MDCservice/EsPiFF/images/cs_weekly/idf_hello_world1.png

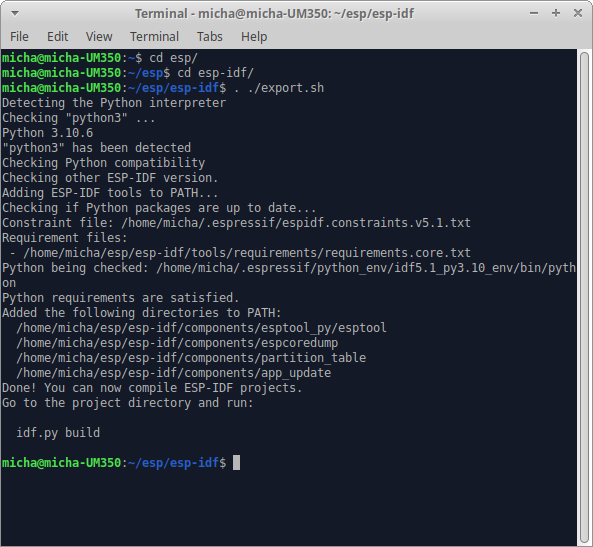
images/cs_weekly/idf_hello_world1.png
