MDCservice/EsPiFF/images/cs_weekly/idf_hello_world2.png

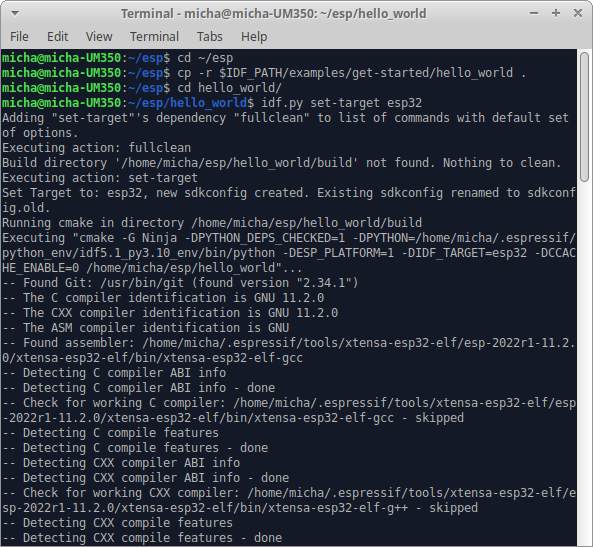
images/cs_weekly/idf_hello_world2.png
