MDCservice/EsPiFF/images/cs_weekly/idf_hello_world3.png

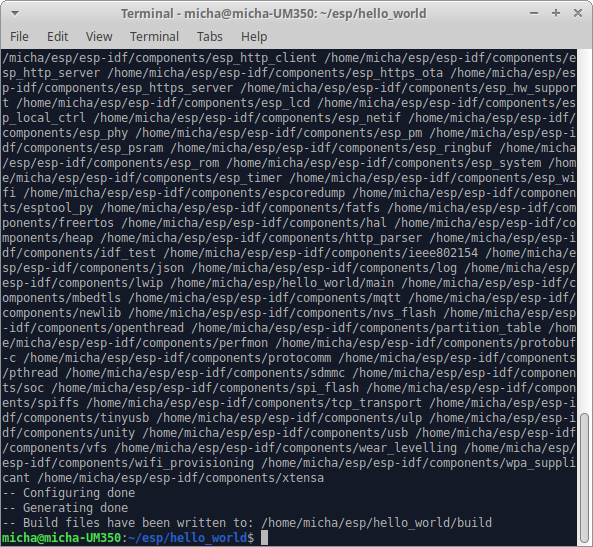
images/cs_weekly/idf_hello_world3.png
