MDCservice/EsPiFF/images/cs_weekly/idf_hello_world4.png

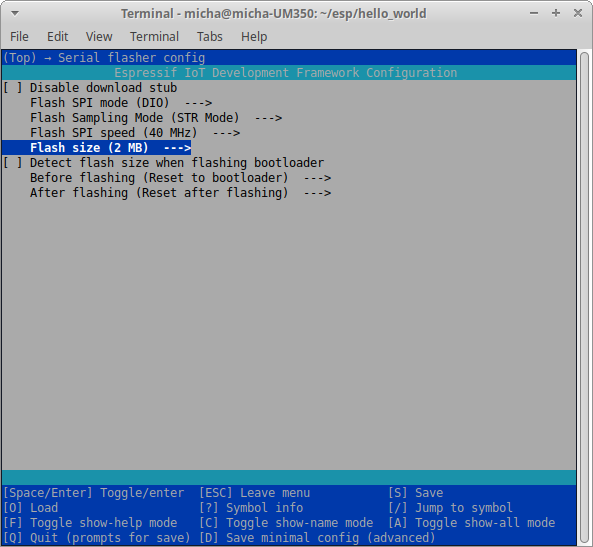
images/cs_weekly/idf_hello_world4.png
