MDCservice/EsPiFF/images/cs_weekly/idf_hello_world6.png

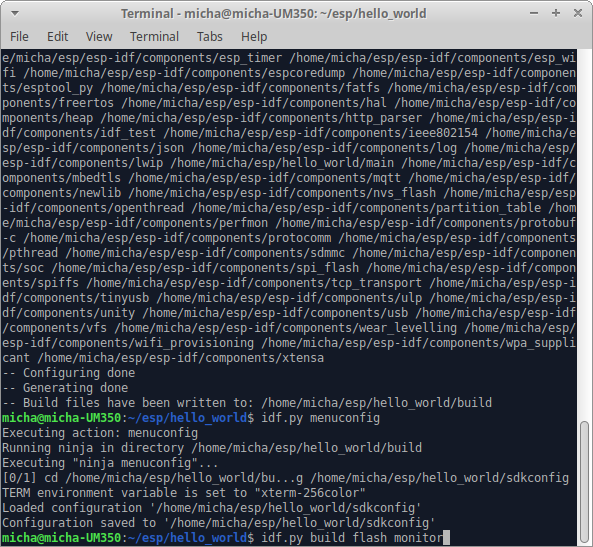
images/cs_weekly/idf_hello_world6.png
