MDCservice/EsPiFF/images/cs_weekly/idf_hello_world7.png

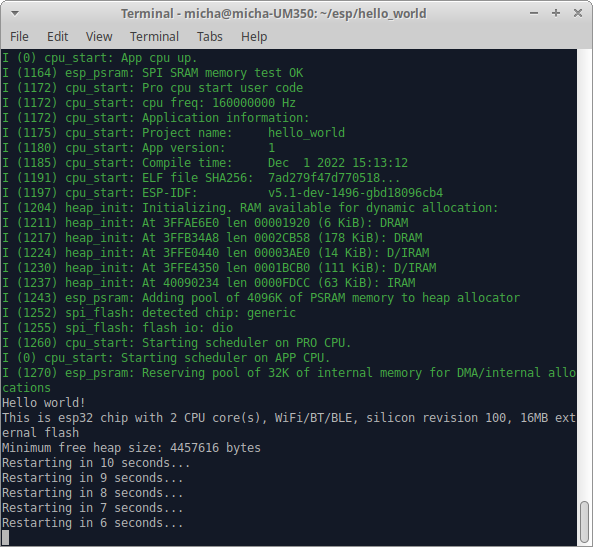
images/cs_weekly/idf_hello_world7.png
