MDCservice/EsPiFF/images/espiff_autoWeiss.jpg

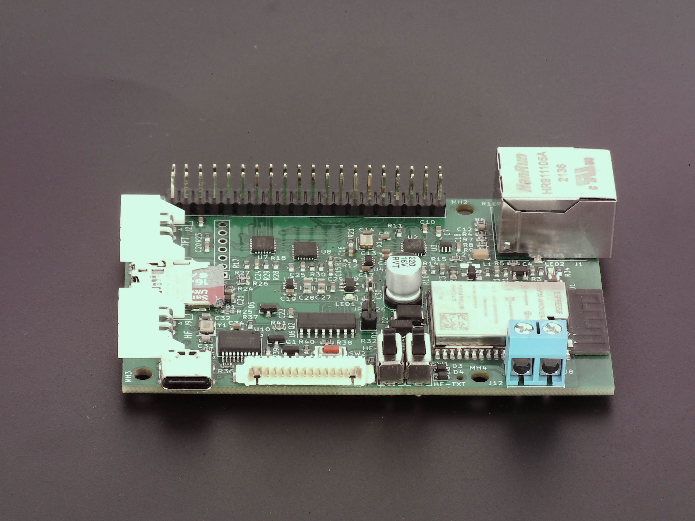
images/espiff_autoWeiss.jpg
