MDCservice/EsPiFF/images/Espiff_boot_nuttx.png

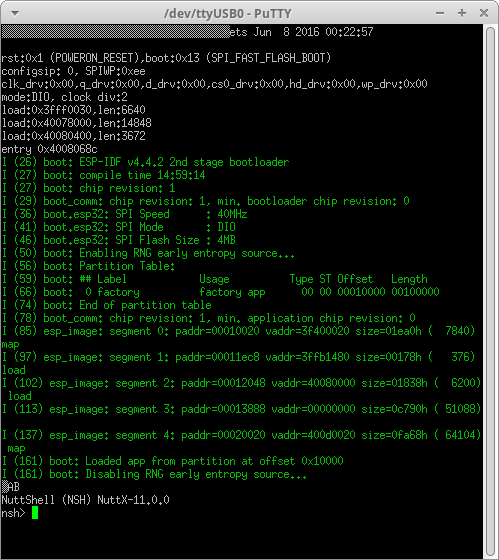
images/Espiff_boot_nuttx.png
