MDCservice/EsPiFF/images/espiff_HMI_horiz.jpg

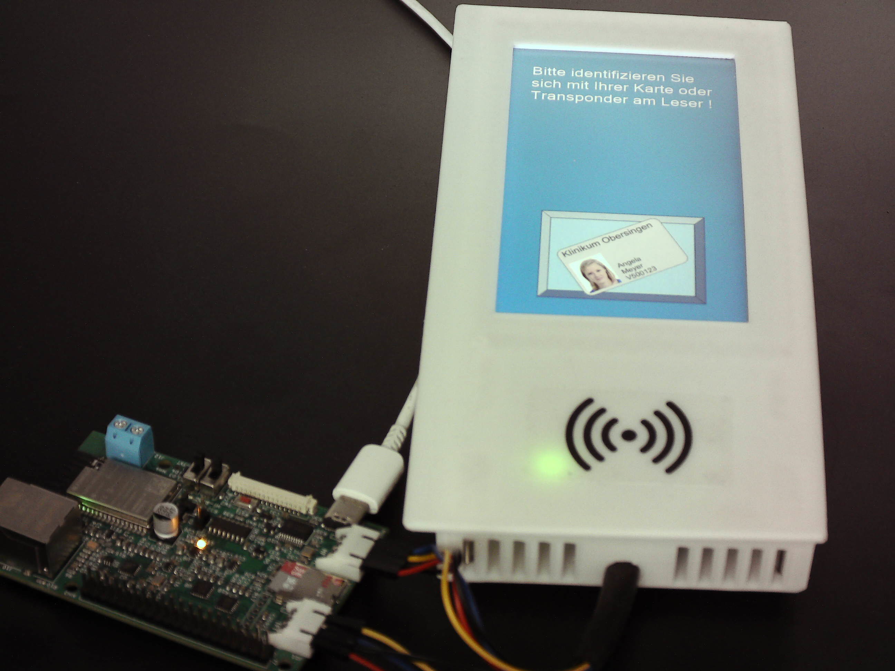
images/espiff_HMI_horiz.jpg
