MDCservice/EsPiFF/images/EsPiFF_PLC_Loop_compare.png

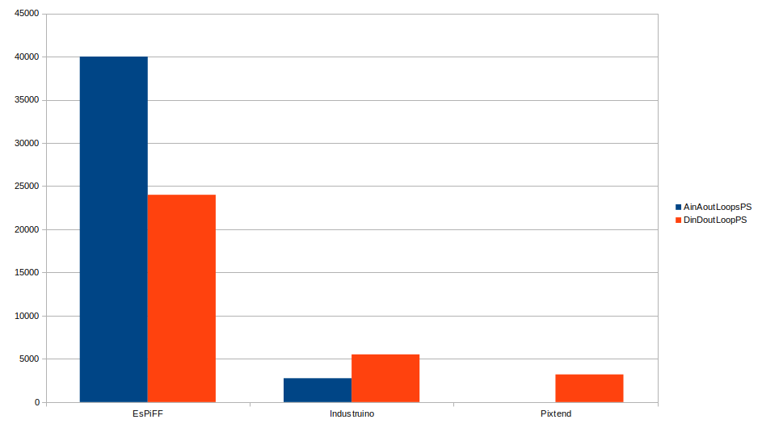
images/EsPiFF_PLC_Loop_compare.png
