MDCservice/EsPiFF/images/espiff_v3_1_annotated.png

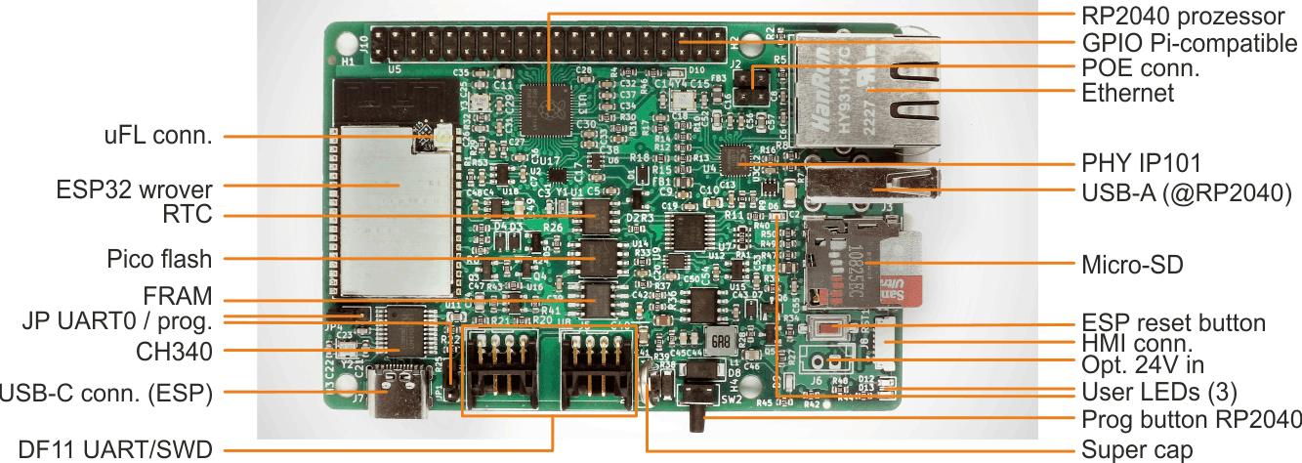
images/espiff_v3_1_annotated.png
