MDCservice/EsPiFF/images/espiff_v3_board-annotated-400.png

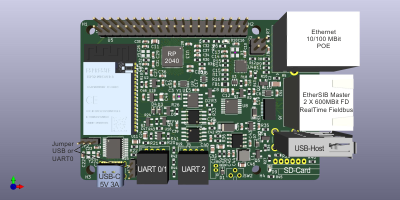
images/espiff_v3_board-annotated-400.png
