MDCservice/EsPiFF/images/espiff_v3_winkel.jpg

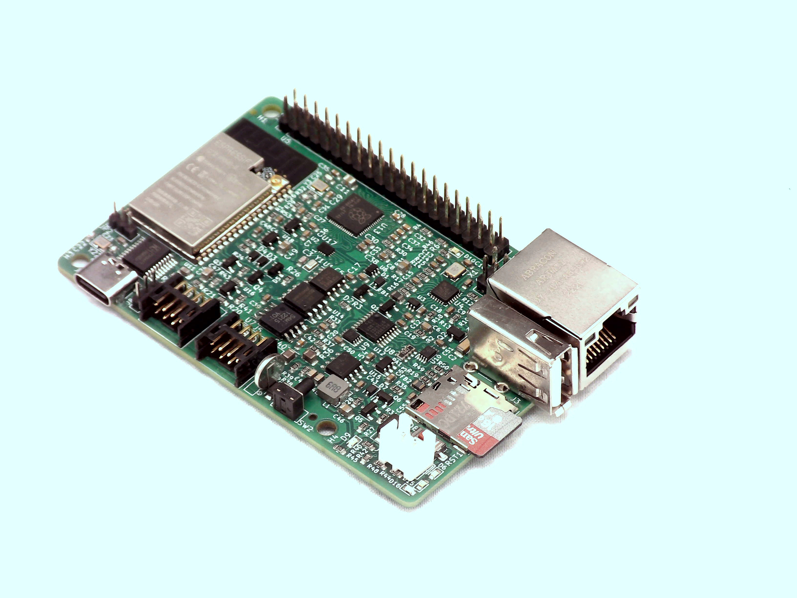
images/espiff_v3_winkel.jpg
