MDCservice/EsPiFF/images/usb_desciptor_c_after_mod.png

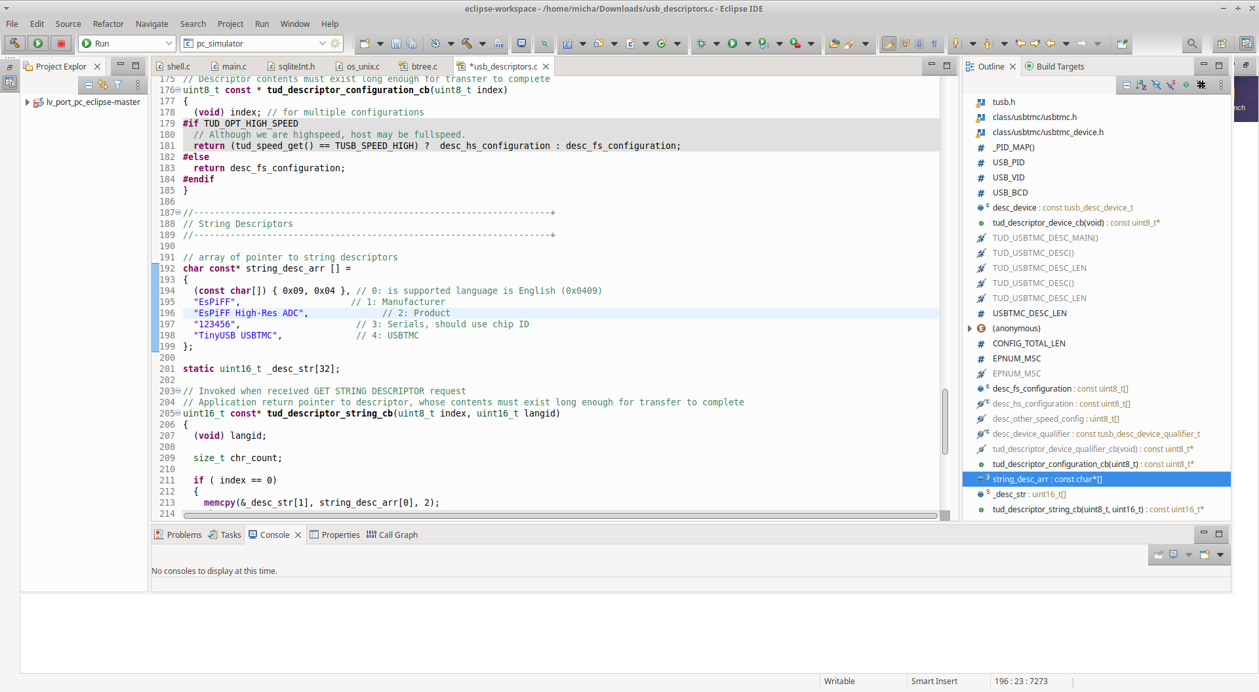
images/usb_desciptor_c_after_mod.png
