MDCservice/EsPiFF/images/v3_1_crowd_supply/espiff_v3.1-angled-0.jpg

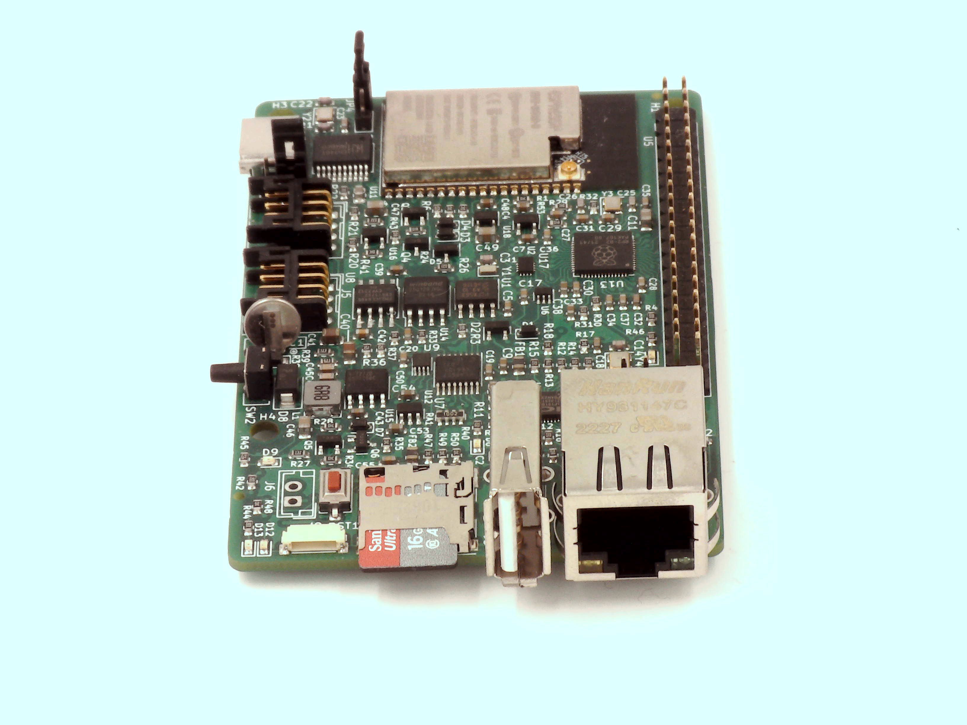
images/v3_1_crowd_supply/espiff_v3.1-angled-0.jpg
