MDCservice/EsPiFF/images/espiff_manualWeiss.jpg

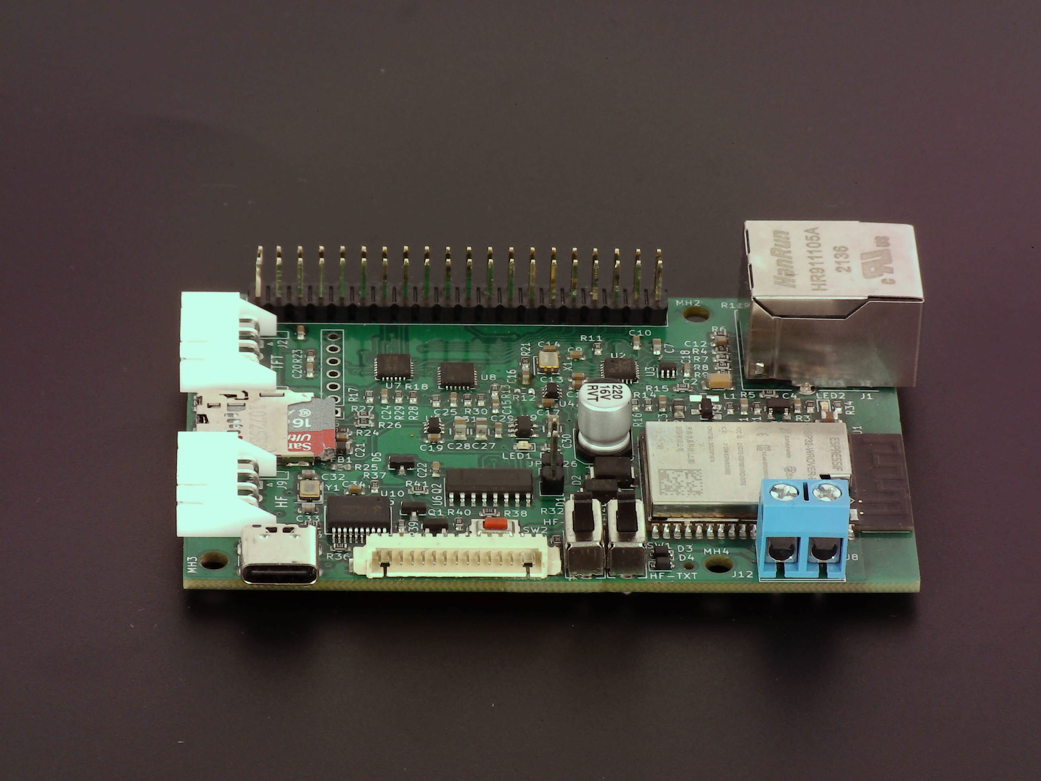
images/espiff_manualWeiss.jpg
