MDCservice/EsPiFF/hardware/espiff_v3_1.kicad_sch

## KiCad design hardware/espiff_v3_1.kicad_sch (2022-10-01)

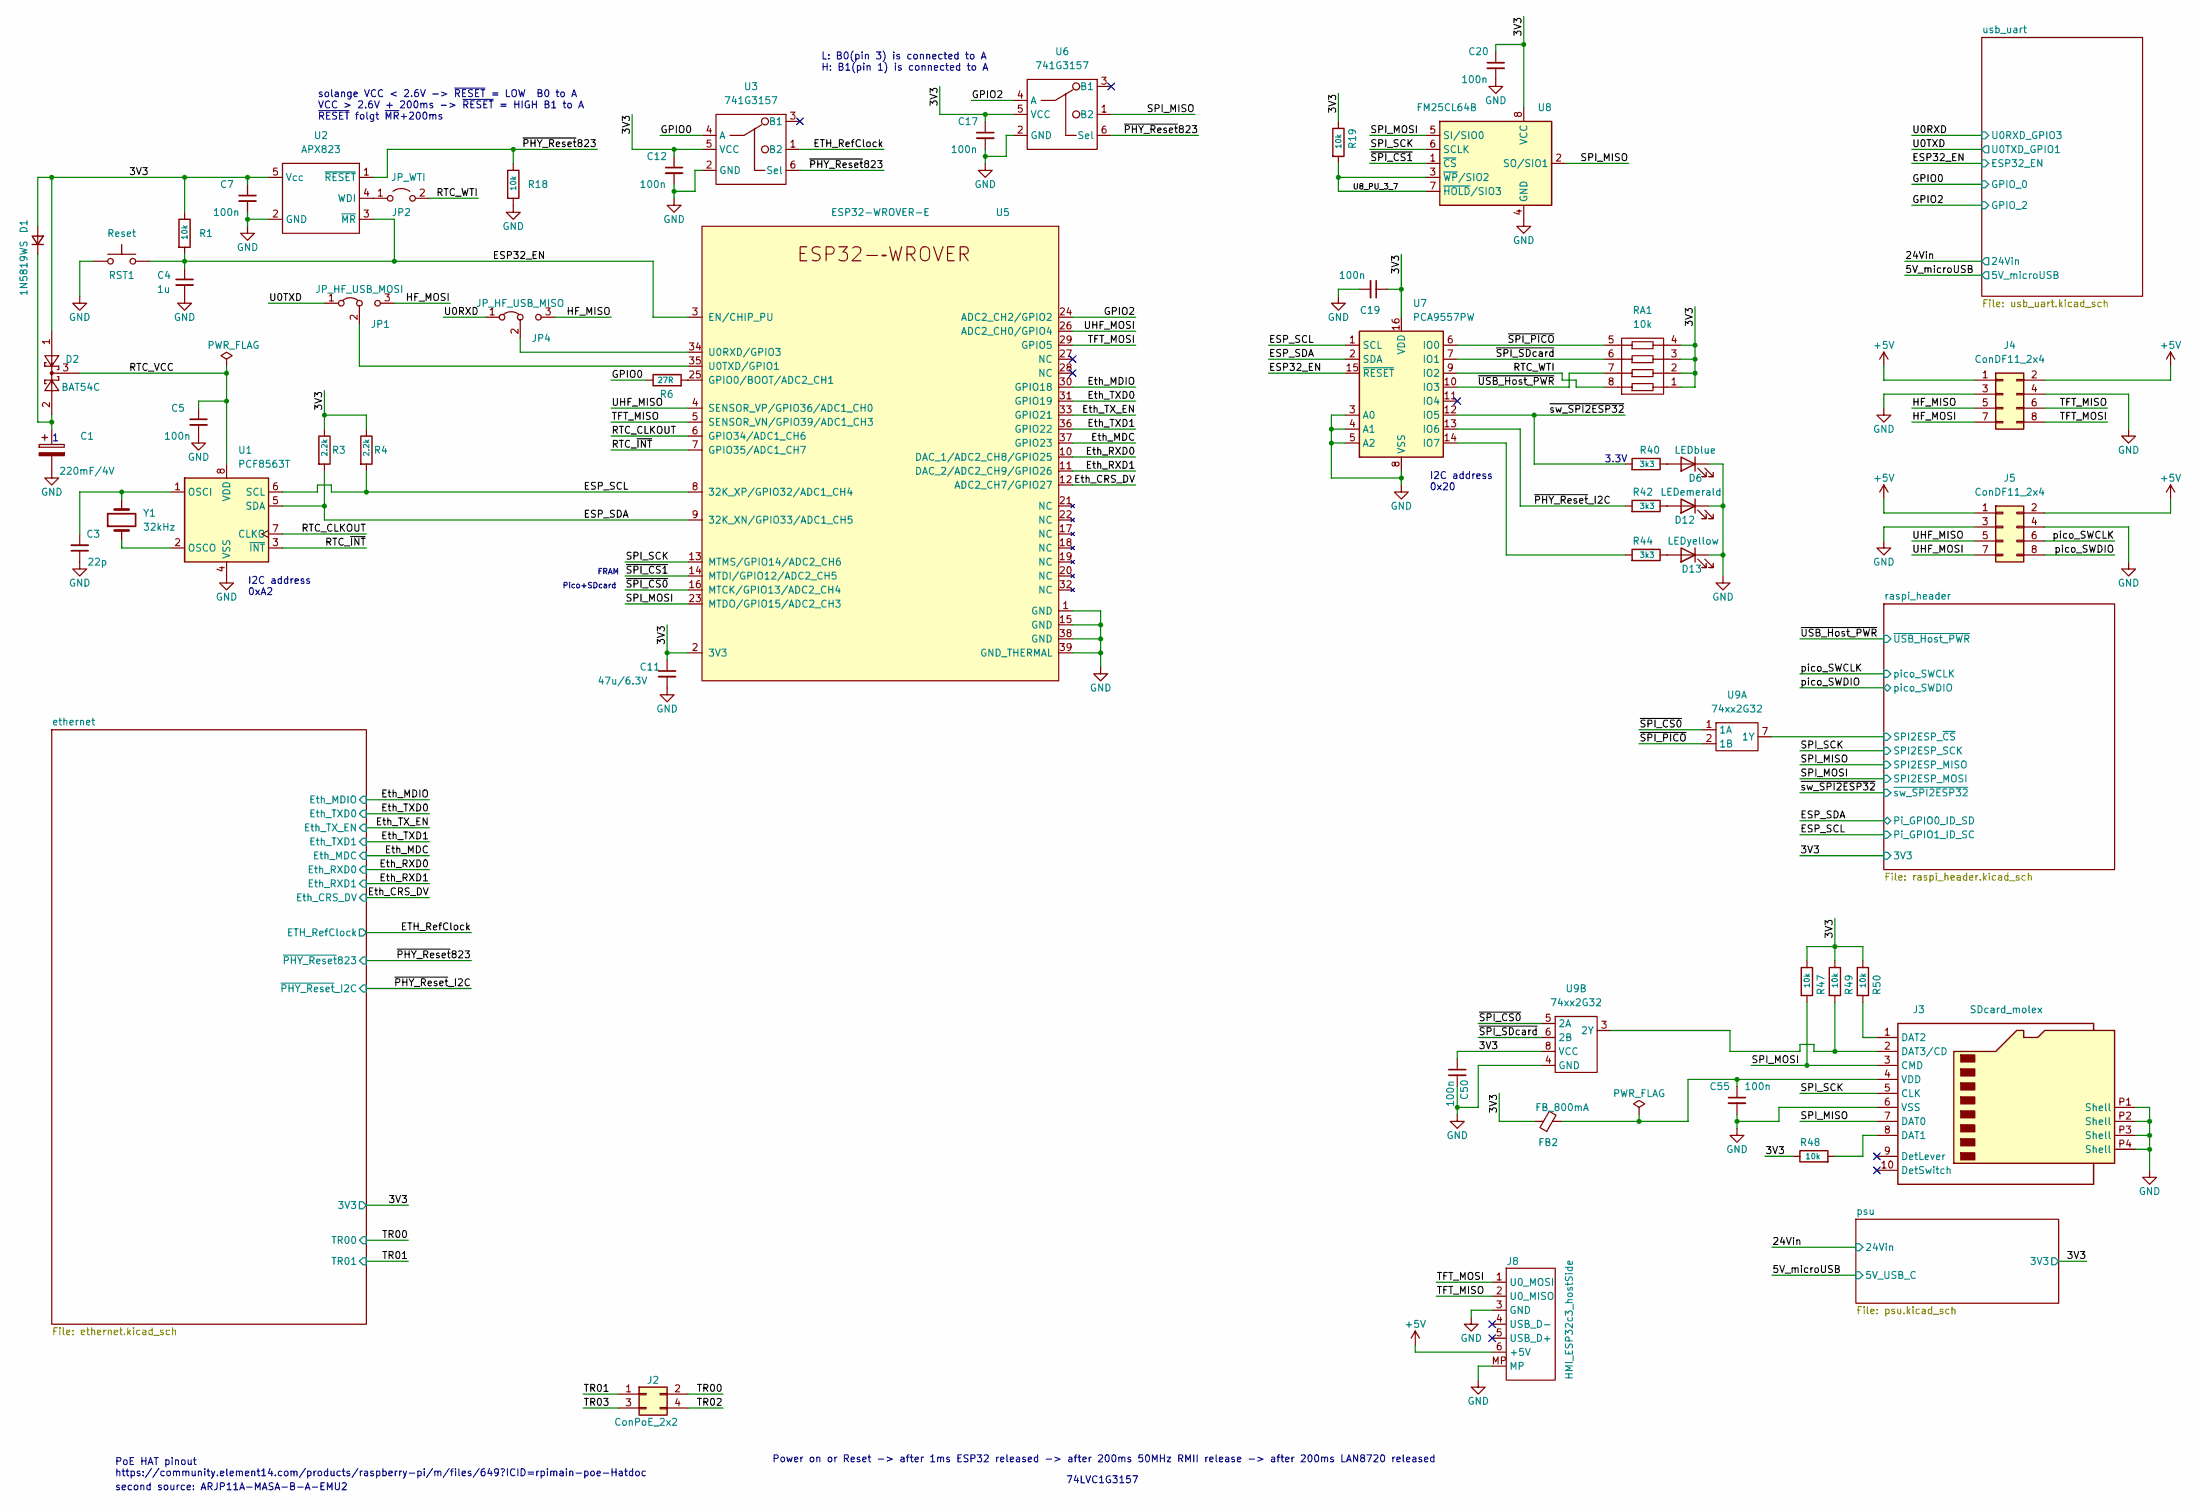
[picture p57: schematic espiff_v3_1.kicad_sch]

Parts:
C1: 220mF/4V; supercap_DMS3R3224R
C3: 22p; C_0603_1608Metric
C4: 1u; C_0603_1608Metric
C5, C7, C12, C17, C19, C20, C50, C55: 100n; C_0603_1608Metric
C11: 47u/6.3V; C_0805_2012Metric
D1: 1N5819WS; D_SOD-323
D2: BAT54C; SOT-23
D6: LEDblue; LED_0603_1608Metric
D12: LEDemerald; LED_0603_1608Metric
D13: LEDyellow; LED_0603_1608Metric
FB2: FB_800mA; R_0805_2012Metric
J2: ConPoE_2x2; PinHeader_2x02_P2.54mm_Vertical
J3: SDcard_molex; MOLEX_503398-1892
J4, J5: ConDF11_2x4; DF11-8DP-2DS(52)
J8: HMI_ESP32c3_hostSide; JST_SUR_SM06B-SURS-TF_1x06-1MP_P0.80mm_Horizontal
JP1: JP_HF_USB_MOSI; PinHeader_1x03_P2.00mm_Vertical
JP2: JP_WTI; SolderJumper-2_P1.3mm_Open_Pad1.0x1.5mm
JP4: JP_HF_USB_MISO; PinHeader_1x03_P2.00mm_Vertical
R1, R18, R19, R47, R48, R49, R50: 10k; R_0603_1608Metric
R3, R4: 2.2k; R_0603_1608Metric
R6: 27R; R_0603_1608Metric
R40, R42, R44: 3k3; R_0603_1608Metric
RA1: 10k; R_Array_Convex_4x0603
RST1: Reset; Btn_KEY-SMD_JCLPCB_C698192
U1: PCF8563T; SOIC-8_3.9x4.9mm_P1.27mm
U2: APX823; SOT-23-5
U3, U6: 741G3157; SOT-363_SC-70-6
U5: ESP32-WROVER-E
U7: PCA9557PW; TSSOP-16_4.4x5mm_P0.65mm
U8: FM25CL64B; SOIC8_W+N_combi
U9: 74xx2G32; VSSOP-8_2.3x2mm_P0.5mm
Y1: 32kHz; Crystal_SMD_2012-2Pin_2.0x1.2mm

Connections:
3V3: C7.1, C11.1, C12.1, C17.1, C19.1, C20.1, C50.1, D1.2 (A), D2.1, FB2.1, R1.1, R3.1, R4.1, R19.1, R47.1, R48.1, R49.1, R50.1, RA1.1, RA1.2, RA1.3, RA1.4, U2.5 (Vcc), U3.5 (VCC), U5.2 (3V3), U6.5 (VCC), U7.16 (VDD), U8.8 (VCC), U9.8 (VCC)
+5V: J4.1, J4.2, J5.1, J5.2, J8.6 (+5V)
ESP32_EN: C4.1, R1.2, RST1.2, U2.3 (~MR), U5.3 (EN/CHIP_PU), U7.15 (~RESET)
ESP_SCL: R4.2, U1.6 (SCL), U5.8 (32K_XP/GPIO32/ADC1_CH4), U7.1 (SCL)
ESP_SDA: R3.2, U1.5 (SDA), U5.9 (32K_XN/GPIO33/ADC1_CH5), U7.2 (SDA)
ETH_RefClock: U3.1 (B2)
Eth_CRS_DV: U5.12 (ADC2_CH7/GPIO27)
Eth_MDC: U5.37 (GPIO23)
Eth_MDIO: U5.30 (GPIO18)
Eth_RXD0: U5.10 (DAC_1/ADC2_CH8/GPIO25)
Eth_RXD1: U5.11 (DAC_2/ADC2_CH9/GPIO26)
Eth_TXD0: U5.31 (GPIO19)
Eth_TXD1: U5.36 (GPIO22)
Eth_TX_EN: U5.33 (GPIO21)
GND: C1.2, C3.1, C4.2, C5.2, C7.2, C11.2, C12.2, C17.2, C19.2, C20.2, C50.2, C55.2, D6.1 (K), D12.1 (K), D13.1 (K), J3.6 (VSS), J3.P1 (Shell), J3.P2 (Shell), J3.P3 (Shell), J3.P4 (Shell), J4.3, J4.4, J5.3, J5.4, J8.3 (GND), J8.MP, R18.2, RST1.1, U1.4 (VSS), U2.2 (GND), U3.2 (GND), U5.1 (GND), U5.15 (GND), U5.38 (GND), U5.39 (GND_THERMAL), U6.2 (GND), U7.3 (A0), U7.4 (A1), U7.5 (A2), U7.8 (VSS), U8.4 (GND), U9.4 (GND)
GPIO0: R6.1, U3.4 (A)
GPIO2: U5.24 (ADC2_CH2/GPIO2), U6.4 (A)
HF_MISO: J4.5, JP4.3 (B)
HF_MOSI: J4.7, JP1.3 (B)
unnamed: C1.1, D1.1 (K), D2.2
unnamed: C3.2, U1.1 (OSCI), Y1.2
unnamed: C55.1, FB2.2, J3.4 (VDD)
unnamed: D6.2 (A), R40.1
unnamed: D12.2 (A), R42.1
unnamed: D13.2 (A), R44.1
unnamed: J3.1 (DAT2), R50.2
unnamed: J3.2 (DAT3/CD), R49.2, U9.3 (2Y)
unnamed: J3.8 (DAT1), R48.2
unnamed: JP1.2 (C), U5.35 (U0TXD/GPIO1)
unnamed: JP2.1 (A), U2.4 (WDI)
unnamed: JP4.2 (C), U5.34 (U0RXD/GPIO3)
unnamed: R6.2, U5.25 (GPIO0/BOOT/ADC2_CH1)
unnamed: R44.2, U7.14 (IO7)
unnamed: U1.2 (OSCO), Y1.1
RTC_CLKOUT: U1.7 (CLKO), U5.6 (GPIO34/ADC1_CH6)
RTC_VCC: C5.1, D2.3, U1.8 (VDD)
RTC_WTI: JP2.2 (B), RA1.8, U7.9 (IO2)
RTC_~INT: U1.3 (~INT), U5.7 (GPIO35/ADC1_CH7)
SPI2ESP_~CS: U9.7 (1Y)
SPI_MISO: J3.7 (DAT0), U6.1 (B2), U8.2 (SO/SIO1)
SPI_MOSI: J3.3 (CMD), R47.2, U5.23 (MTDO/GPIO15/ADC2_CH3), U8.5 (SI/SIO0)
SPI_SCK: J3.5 (CLK), U5.13 (MTMS/GPIO14/ADC2_CH6), U8.6 (SCLK)
TFT_MISO: J4.6, J8.2 (U0_MISO), U5.5 (SENSOR_VN/GPIO39/ADC1_CH3)
TFT_MOSI: J4.8, J8.1 (U0_MOSI), U5.29 (GPIO5)
TR00: J2.2
TR01: J2.1
TR02: J2.4
TR03: J2.3
U0RXD: JP4.1 (A)
U0TXD: JP1.1 (A)
U8_PU_3_7: R19.2, U8.3 (~WP/SIO2), U8.7 (~HOLD/SIO3)
UHF_MISO: J5.5, U5.4 (SENSOR_VP/GPIO36/ADC1_CH0)
UHF_MOSI: J5.7, U5.26 (ADC2_CH0/GPIO4)
pico_SWCLK: J5.6
pico_SWDIO: J5.8
~PHY_Reset823: R18.1, U2.1 (~RESET), U3.6 (Sel), U6.6 (Sel)
~PHY_Reset_I2C: R42.2, U7.13 (IO6)
~SPI_CS0: U5.16 (MTCK/GPIO13/ADC2_CH4), U9.1 (1A), U9.5 (2A)
~SPI_CS1: U5.14 (MTDI/GPIO12/ADC2_CH5), U8.1 (~CS)
~SPI_PICO: RA1.5, U7.6 (IO0), U9.2 (1B)
~SPI_SDcard: RA1.6, U7.7 (IO1), U9.6 (2B)
~USB_Host_PWR: RA1.7, U7.10 (IO3)
~sw_SPI2ESP32: R40.2, U7.12 (IO5)

Notes on the sheet:
Power on or Reset -> after 1ms ESP32 released -> after 200ms 50MHz RMII release -> after 200ms LAN8720 released
Pico+SDcard
3.3V
I2C address 0x20
solange VCC < 2.6V -> ~{RESET} = LOW B0 to A VCC > 2.6V + 200ms -> ~{RESET} = HIGH B1 to A ~{RESET} folgt ~{MR}+200ms
PoE HAT pinout https://community.element14.com/products/raspberry-pi/m/files/649?ICID=rpimain-poe-Hatdoc
second source: ARJP11A-MASA-B-A-EMU2
I2C address 0xA2
FRAM
L: B0(pin 3) is connected to A H: B1(pin 1) is connected to A
74LVC1G3157
