MDCservice/EsPiFF/hardware/ethernet.kicad_sch

## KiCad design hardware/ethernet.kicad_sch (2022-10-01)

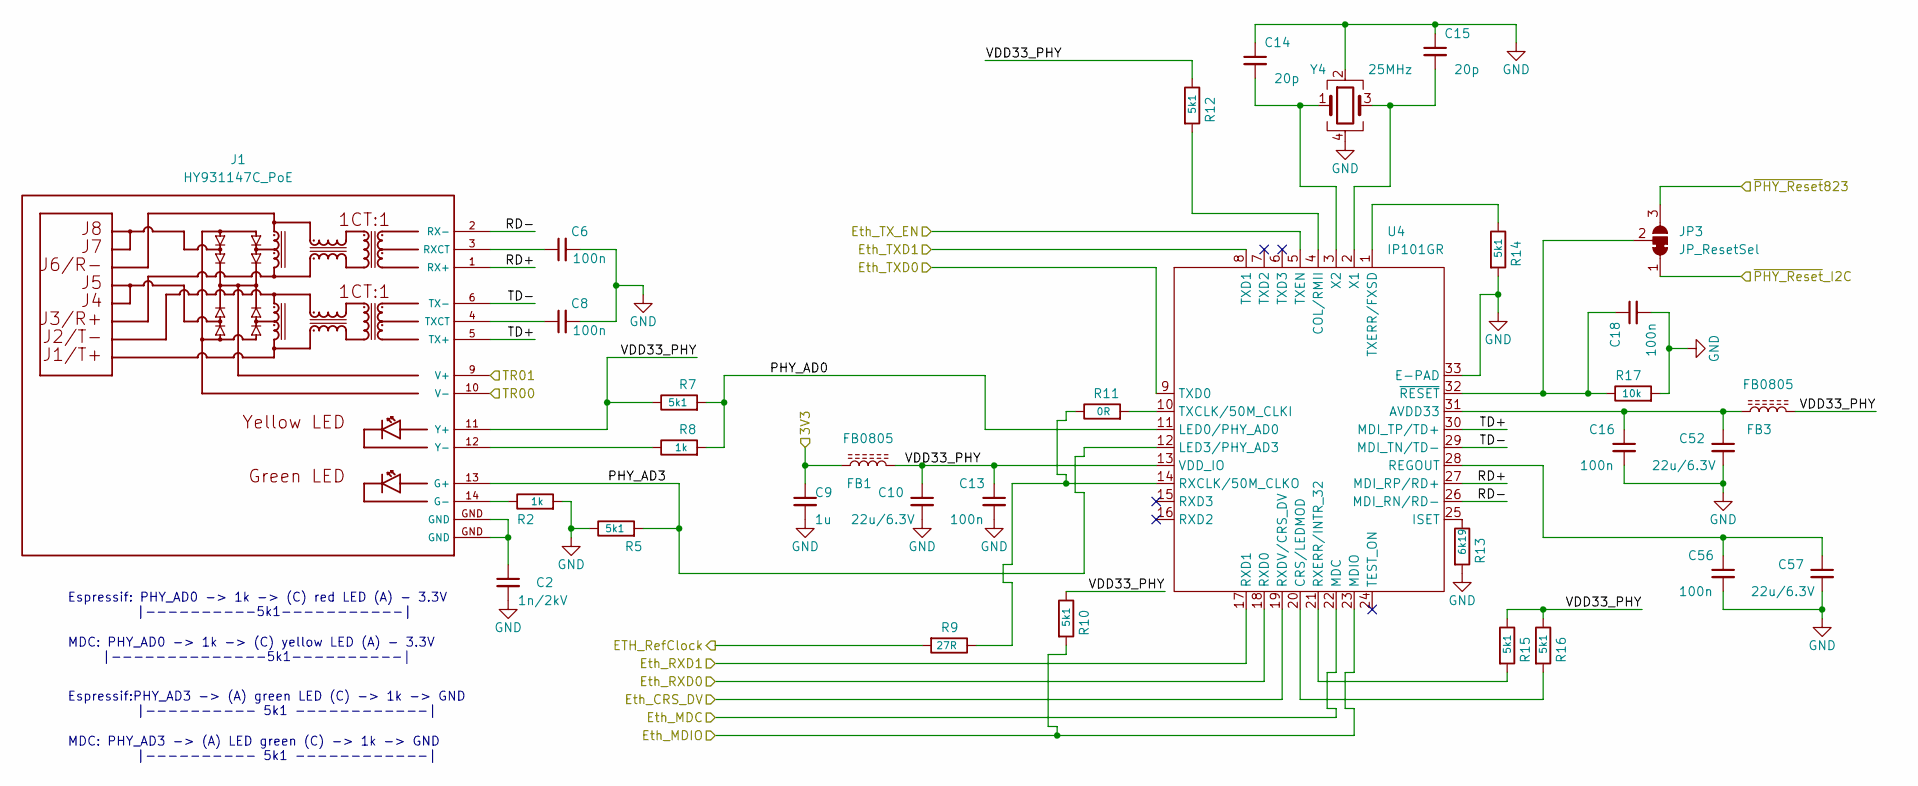
[picture p58: schematic ethernet.kicad_sch]

Parts:
C2: 1n/2kV; C_1206_3216Metric
C6, C8, C13, C16, C18, C56: 100n; C_0603_1608Metric
C9: 1u; C_0603_1608Metric
C10, C52, C57: 22u/6.3V; C_0805_2012Metric
C14, C15: 20p; C_0603_1608Metric
FB1, FB3: FB0805; R_0805_2012Metric
J1: HY931147C_PoE; HY931147C
JP3: JP_ResetSel; SolderJumper-3_P1.3mm_Bridged12_RoundedPad1.0x1.5mm
R2, R8: 1k; R_0603_1608Metric
R5, R7, R10, R12, R14, R15, R16: 5k1; R_0603_1608Metric
R9: 27R; R_0603_1608Metric
R11: 0R; R_0603_1608Metric
R13: 6k19; R_0603_1608Metric
R17: 10k; R_0603_1608Metric
U4: IP101GR; QFN-32-1EP_4x4mm_P0.4mm_EP2.65x2.65mm
Y4: 25MHz; Crystal_SMD_3225-4Pin_3.2x2.5mm

Connections:
3V3: C9.1, FB1.1
ETH_RefClock: R9.2
Eth_CRS_DV: U4.19 (RXDV/CRS_DV)
Eth_MDC: U4.22 (MDC)
Eth_MDIO: R10.2, U4.23 (MDIO)
Eth_RXD0: U4.18 (RXD0)
Eth_RXD1: U4.17 (RXD1)
Eth_TXD0: U4.9 (TXD0)
Eth_TXD1: U4.8 (TXD1)
Eth_TX_EN: U4.5 (TXEN)
GND: C2.2, C6.2, C8.2, C9.2, C10.2, C13.2, C14.1, C15.1, C16.2, C18.2, C52.2, C56.2, C57.2, R2.2, R5.1, R13.2, R14.2, R17.2, U4.33 (E-PAD), Y4.2, Y4.4
unnamed: C2.1, J1.GND
unnamed: C6.1, J1.3 (RXCT)
unnamed: C8.1, J1.4 (TXCT)
unnamed: C14.2, U4.3 (X2), Y4.1
unnamed: C15.2, U4.2 (X1), Y4.3
unnamed: C16.1, C52.1, FB3.1, U4.31 (AVDD33)
unnamed: C18.1, JP3.2 (C), R17.1, U4.32 (~RESET)
unnamed: C56.1, C57.1, U4.28 (REGOUT)
unnamed: J1.12 (Y-), R8.1
unnamed: J1.14 (G-), R2.1
unnamed: R9.1, R11.1, U4.14 (RXCLK/50M_CLKO)
unnamed: R11.2, U4.10 (TXCLK/50M_CLKI)
unnamed: R12.2, U4.4 (COL/RMII)
unnamed: R13.1, U4.25 (ISET)
unnamed: R14.1, U4.1 (TXERR/FXSD)
unnamed: R15.2, U4.21 (RXERR/INTR_32)
unnamed: R16.2, U4.20 (CRS/LEDMOD)
PHY_AD0: R7.2, R8.2, U4.11 (LED0/PHY_AD0)
PHY_AD3: J1.13 (G+), R5.2, U4.12 (LED3/PHY_AD3)
RD+: J1.1 (RX+), U4.27 (MDI_RP/RD+)
RD-: J1.2 (RX-), U4.26 (MDI_RN/RD-)
TD+: J1.5 (TX+), U4.30 (MDI_TP/TD+)
TD-: J1.6 (TX-), U4.29 (MDI_TN/TD-)
TR00: J1.10 (V-)
TR01: J1.9 (V+)
VDD33_PHY: C10.1, C13.1, FB1.2, FB3.2, J1.11 (Y+), R7.1, R10.1, R12.1, R15.1, R16.1, U4.13 (VDD_IO)
~PHY_Reset823: JP3.3 (B)
~PHY_Reset_I2C: JP3.1 (A)

Notes on the sheet:
Espressif: PHY_AD0 -> 1k -> (C) red LED (A) - 3.3V |----------5k1-----------|
Espressif:PHY_AD3 -> (A) green LED (C) -> 1k -> GND |---------- 5k1 ------------|
MDC: PHY_AD3 -> (A) LED green (C) -> 1k -> GND |---------- 5k1 ------------|
MDC: PHY_AD0 -> 1k -> (C) yellow LED (A) - 3.3V |--------------5k1----------|
