MDCservice/EsPiFF/hardware/psu.kicad_sch

## KiCad design hardware/psu.kicad_sch (2022-10-01)

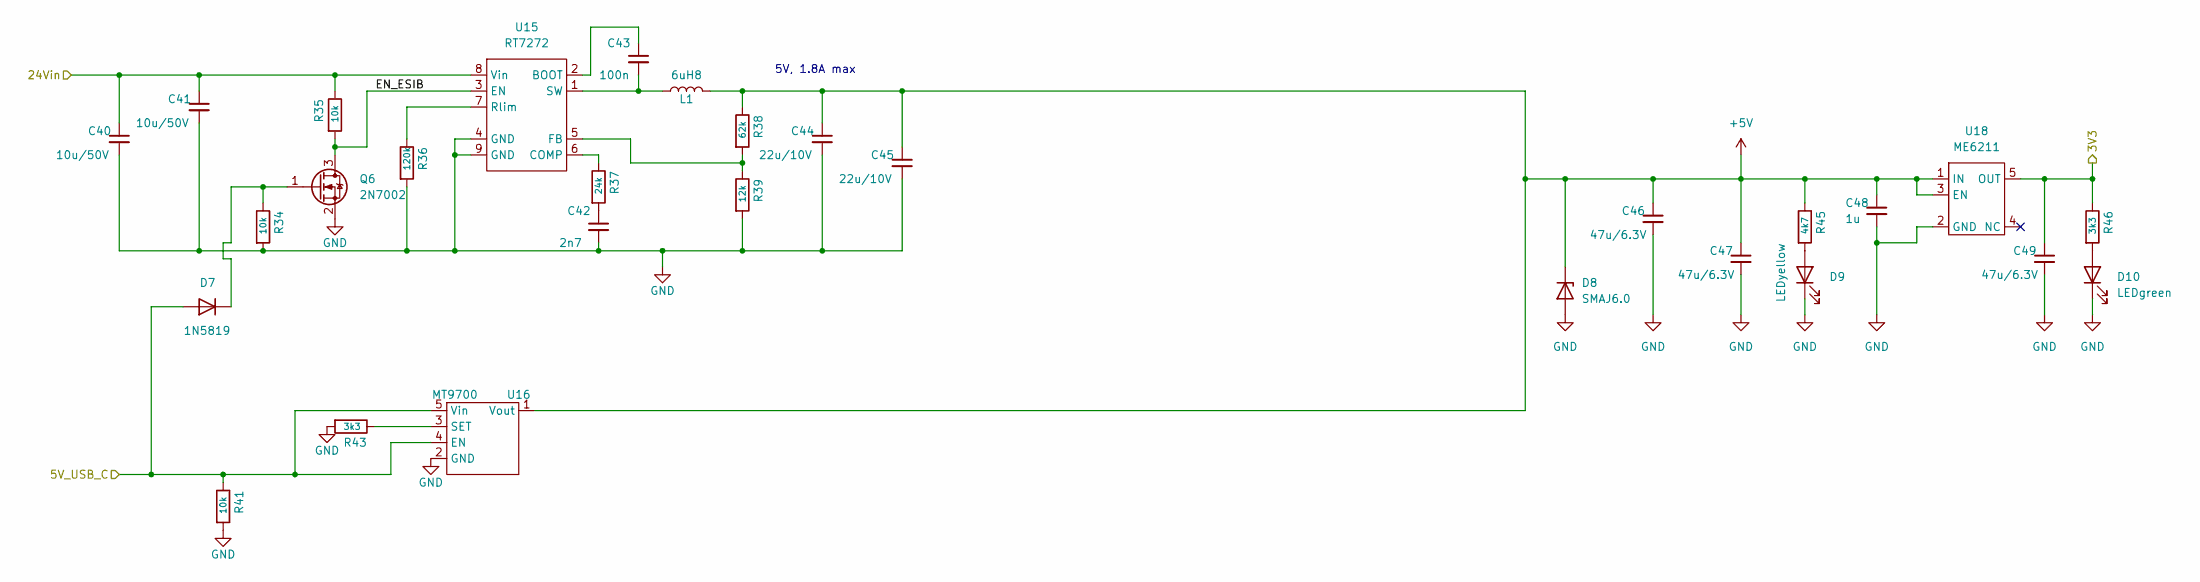
[picture p59: schematic psu.kicad_sch]

Parts:
C40, C41: 10u/50V; C_0805_2012Metric
C42: 2n7; C_0603_1608Metric
C43: 100n; C_0603_1608Metric
C44, C45: 22u/10V; C_0603_1608Metric
C46, C47, C49: 47u/6.3V; C_0805_2012Metric
C48: 1u; C_0603_1608Metric
D7: 1N5819; D_SOD-323
D8: SMAJ6.0; D_SMA
D9: LEDyellow; LED_0603_1608Metric
D10: LEDgreen; LED_0603_1608Metric
L1: 6uH8; L_Bourns-SRN4018
Q6: 2N7002; SOT-23
R34, R35, R41: 10k; R_0603_1608Metric
R36: 120k; R_0603_1608Metric
R37: 24k; R_0603_1608Metric
R38: 62k; R_0603_1608Metric
R39: 12k; R_0603_1608Metric
R43, R46: 3k3; R_0603_1608Metric
R45: 4k7; R_0603_1608Metric
U15: RT7272; SOIC8-1EP_3.9x4.9mm_P1.27_ThermalVias
U16: MT9700; SOT-23-5
U18: ME6211; SOT-23-5

Connections:
3V3: C49.1, R46.1, U18.5 (OUT)
5V_USB_C: D7.2 (A), R41.1, U16.4 (EN), U16.5 (Vin)
24Vin: C40.1, C41.1, R35.1, U15.8 (Vin)
+5V: C44.1, C45.1, C46.1, C47.1, C48.1, D8.1 (K), L1.2, R38.1, R45.1, U16.1 (Vout), U18.1 (IN), U18.3 (EN)
EN_ESIB: Q6.3 (D), R35.2, U15.3 (EN)
GND: C40.2, C41.2, C42.2, C44.2, C45.2, C46.2, C47.2, C48.2, C49.2, D8.2 (A), D9.1 (K), D10.1 (K), Q6.2 (S), R34.2, R36.2, R39.2, R41.2, R43.2, U15.4 (GND), U15.9 (GND), U16.2 (GND), U18.2 (GND)
unnamed: C42.1, R37.2
unnamed: C43.1, U15.2 (BOOT)
unnamed: C43.2, L1.1, U15.1 (SW)
unnamed: D7.1 (K), Q6.1 (G), R34.1
unnamed: D9.2 (A), R45.2
unnamed: D10.2 (A), R46.2
unnamed: R36.1, U15.7 (Rlim)
unnamed: R37.1, U15.6 (COMP)
unnamed: R38.2, R39.1, U15.5 (FB)
unnamed: R43.1, U16.3 (SET)

Notes on the sheet:
5V, 1.8A max
