MDCservice/EsPiFF/hardware/raspi_header.kicad_sch

## KiCad design hardware/raspi_header.kicad_sch (2022-10-01)

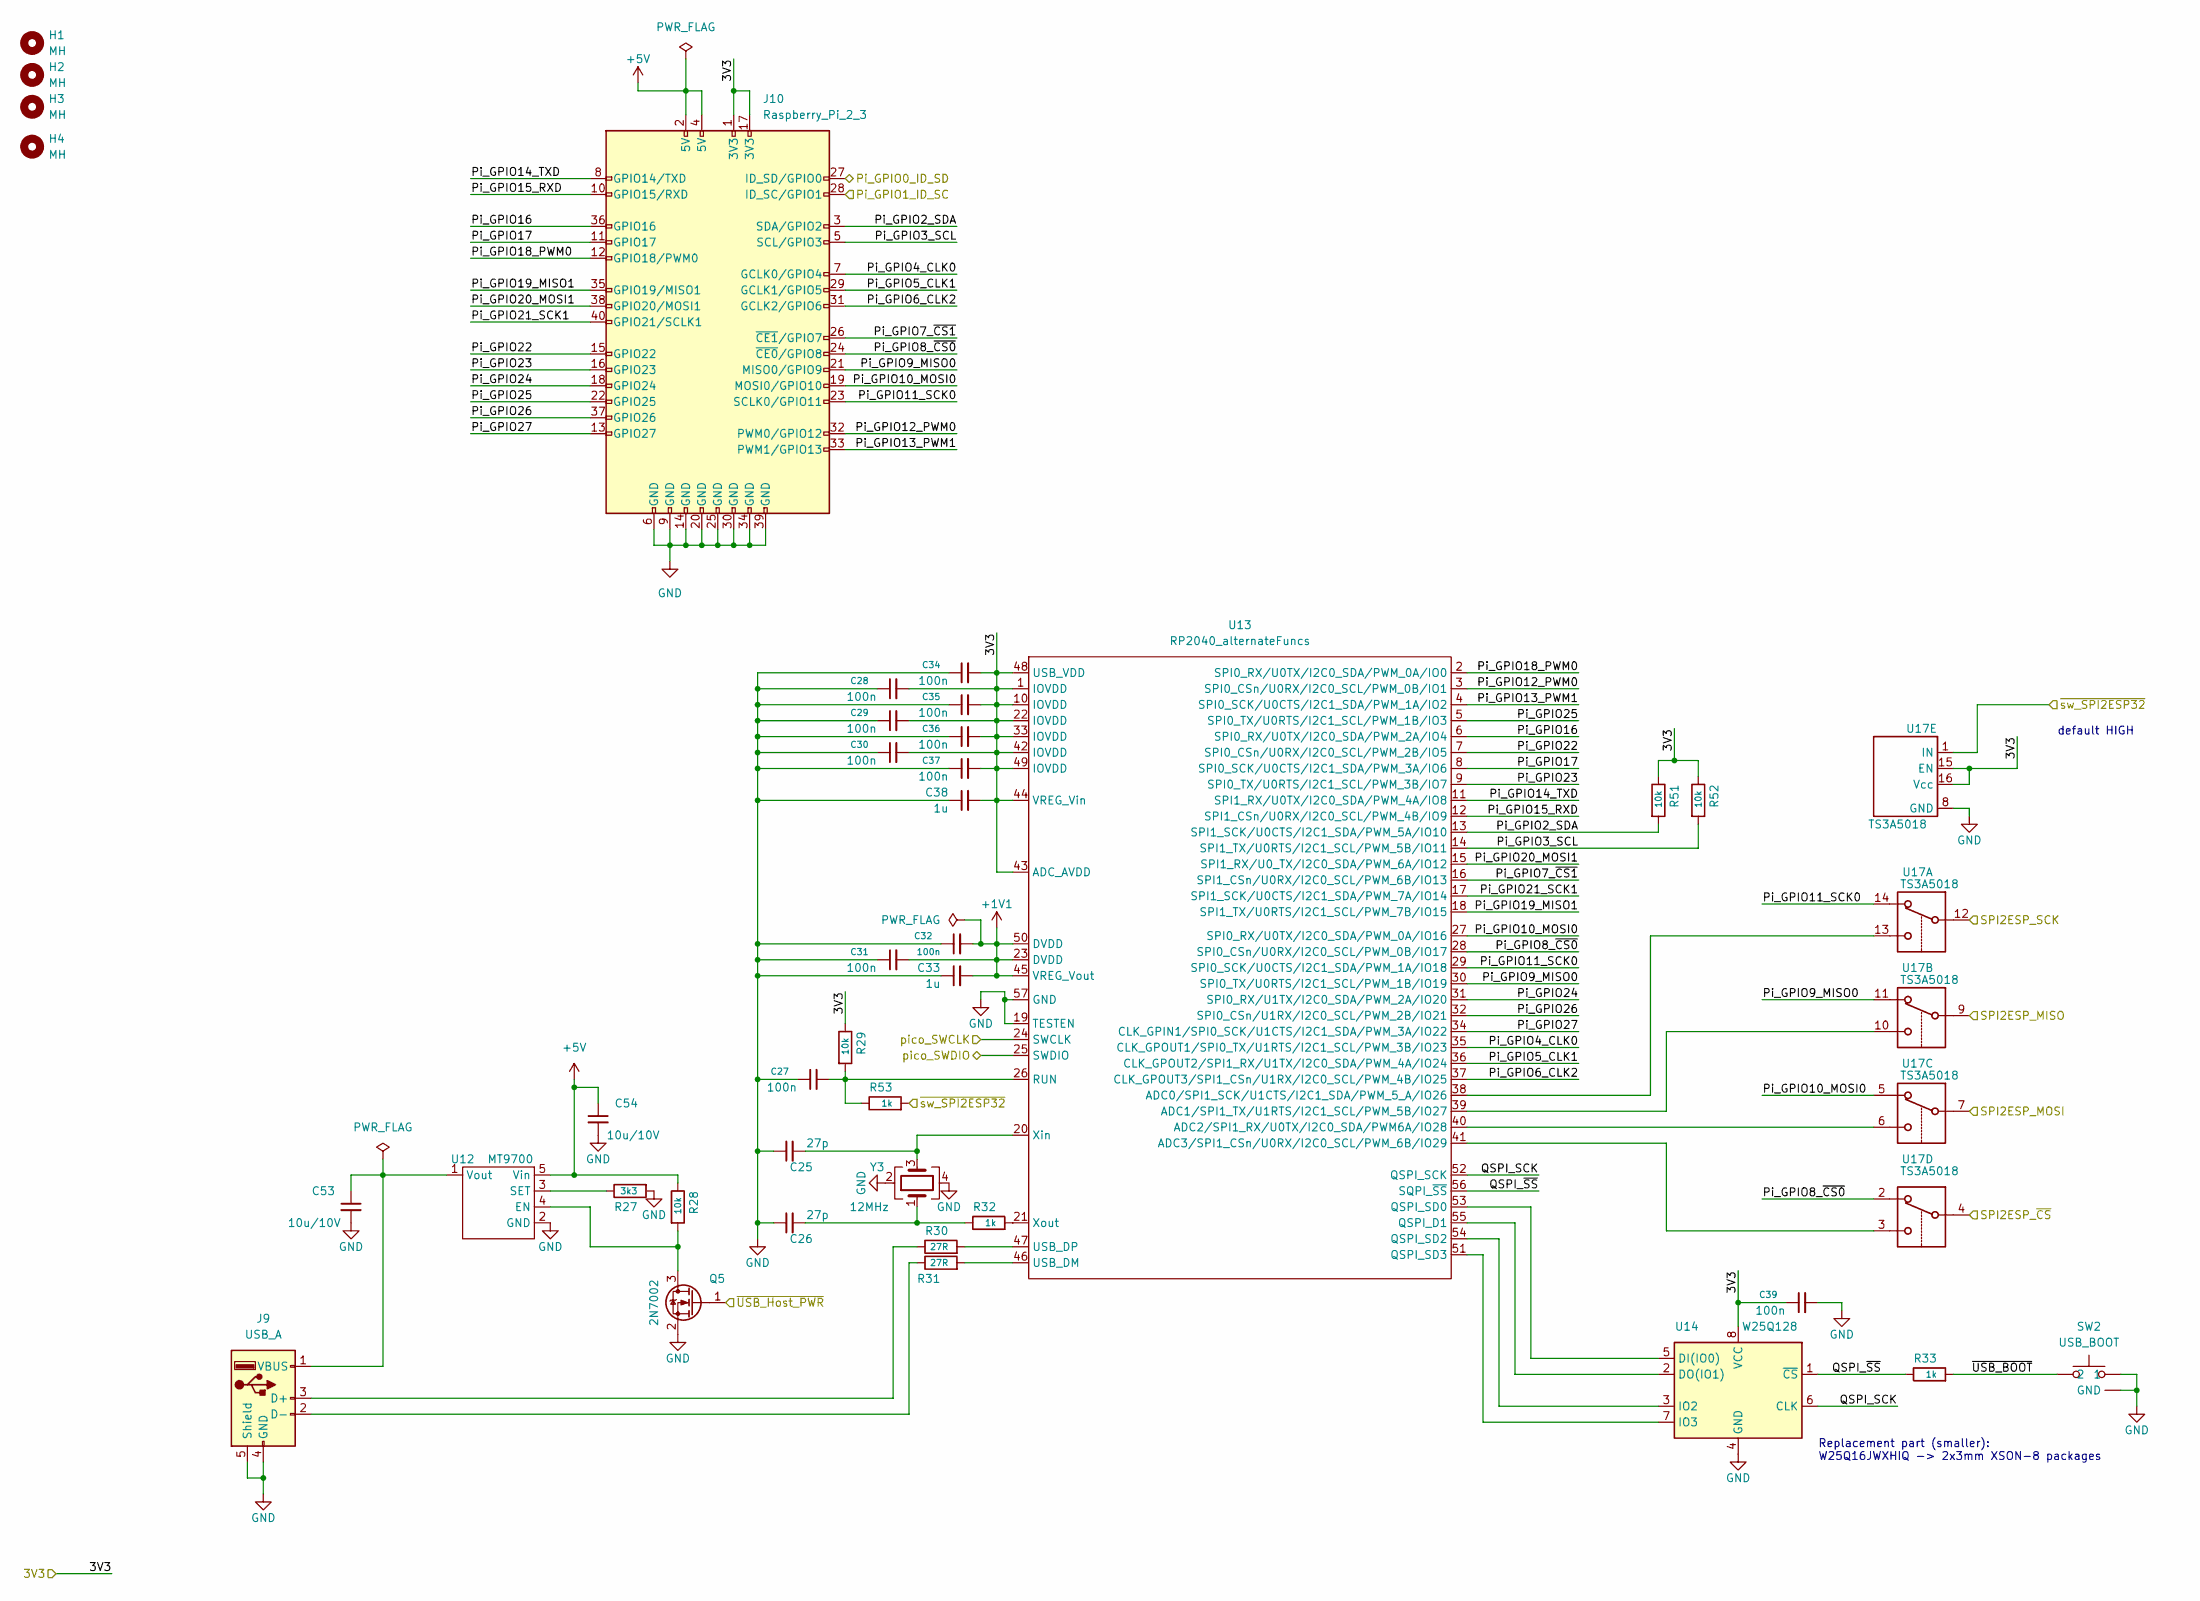
[picture p60: schematic raspi_header.kicad_sch]

Parts:
C25, C26: 27p; C_0603_1608Metric
C27, C28, C29, C30, C31, C32, C34, C35, C36, C37, C39: 100n; C_0603_1608Metric
C33, C38: 1u; C_0603_1608Metric
C53, C54: 10u/10V; C_0603_1608Metric
H1, H2, H3, H4: MH; MountingHole_M3_3.2mm
J9: USB_A; USB_A_C26235
J10: Raspberry_Pi_2_3; PinHeader_2x20_P2.54mm_Vertical
Q5: 2N7002; SOT-23
R27: 3k3; R_0603_1608Metric
R28, R29, R51, R52: 10k; R_0603_1608Metric
R30, R31: 27R; R_0603_1608Metric
R32, R33, R53: 1k; R_0603_1608Metric
SW2: USB_BOOT; Btn_TC-1109DE-C-F
U12: MT9700; SOT-23-5
U13: RP2040_alternateFuncs; QFN56_ThermalVias_0.3
U14: W25Q128; SOIC8_5.23x5.23mm_P1.27mm_mdc
U17: TS3A5018; UQFN-16_1.8x2.6_P0.4mm
Y3: 12MHz; Crystal_SMD_2520-4Pin_2.5x2.0mm

Connections:
3V3: C28.2, C29.2, C30.2, C34.2, C35.2, C36.2, C37.2, C38.2, C39.1, J10.1 (3V3), J10.17 (3V3), R29.1, R51.1, R52.1, U13.1 (IOVDD), U13.10 (IOVDD), U13.22 (IOVDD), U13.33 (IOVDD), U13.42 (IOVDD), U13.43 (ADC_AVDD), U13.44 (VREG_Vin), U13.48 (USB_VDD), U13.49 (IOVDD), U14.8 (VCC), U17.15 (EN), U17.16 (Vcc)
+1V1: C31.2, C32.2, C33.2, U13.23 (DVDD), U13.45 (VREG_Vout), U13.50 (DVDD)
+5V: C54.1, J10.2 (5V), J10.4 (5V), R28.1, U12.5 (Vin)
GND: C25.1, C26.1, C27.1, C28.1, C29.1, C30.1, C31.1, C32.1, C33.1, C34.1, C35.1, C36.1, C37.1, C38.1, C39.2, C53.2, C54.2, J9.4 (GND), J9.5 (Shield), J10.6 (GND), J10.9 (GND), J10.14 (GND), J10.20 (GND), J10.25 (GND), J10.30 (GND), J10.34 (GND), J10.39 (GND), Q5.2 (S), R27.2, SW2.1, SW2.3 (GND), U12.2 (GND), U13.19 (TESTEN), U13.57 (GND), U14.4 (GND), U17.8 (GND), Y3.2, Y3.4
unnamed: C25.2, U13.20 (Xin), Y3.3
unnamed: C26.2, R32.1, Y3.1
unnamed: C27.2, R29.2, R53.1, U13.26 (RUN)
unnamed: C53.1, J9.1 (VBUS), U12.1 (Vout)
unnamed: J9.2 (D-), R31.1
unnamed: J9.3 (D+), R30.1
unnamed: Q5.3 (D), R28.2, U12.4 (EN)
unnamed: R27.1, U12.3 (SET)
unnamed: R30.2, U13.47 (USB_DP)
unnamed: R31.2, U13.46 (USB_DM)
unnamed: R32.2, U13.21 (Xout)
unnamed: U13.38 (ADC0/SPI1_SCK/U1CTS/I2C1_SDA/PWM_5_A/IO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), U17.13
unnamed: U13.39 (ADC1/SPI1_TX/U1RTS/I2C1_SCL/PWM_5B/IO27), U17.10
unnamed: U13.40 (ADC2/SPI1_RX/U0TX/I2C0_SDA/PWM6A/IO28), U17.6
unnamed: U13.41 (ADC3/SPI1_CSn/U0RX/I2C0_SCL/PWM_6B/IO29), U17.3
unnamed: U13.51 (QSPI_SD3), U14.7 (IO3)
unnamed: U13.53 (QSPI_SD0), U14.5 (DI(IO0))
unnamed: U13.54 (QSPI_SD2), U14.3 (IO2)
unnamed: U13.55 (QSPI_D1), U14.2 (DO(IO1))
Pi_GPIO0_ID_SD: J10.27 (ID_SD/GPIO0)
Pi_GPIO1_ID_SC: J10.28 (ID_SC/GPIO1)
Pi_GPIO2_SDA: J10.3 (SDA/GPIO2), R51.2, U13.13 (SPI1_SCK/U0CTS/I2C1_SDA/PWM_5A/IO10)
Pi_GPIO3_SCL: J10.5 (SCL/GPIO3), R52.2, U13.14 (SPI1_TX/U0RTS/I2C1_SCL/PWM_5B/IO11)
Pi_GPIO4_CLK0: J10.7 (GCLK0/GPIO4), U13.35 (CLK_GPOUT1/SPI0_TX/U1RTS/I2C1_SCL/PWM_3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)
Pi_GPIO5_CLK1: J10.29 (GCLK1/GPIO5), U13.36 (CLK_GPOUT2/SPI1_RX/U1TX/I2C0_SDA/PWM_4A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)
Pi_GPIO6_CLK2: J10.31 (GCLK2/GPIO6), U13.37 (CLK_GPOUT3/SPI1_CSn/U1RX/I2C0_SCL/PWM_4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)
Pi_GPIO7_~CS1: J10.26 (~CE1/GPIO7), U13.16 (SPI1_CSn/U0RX/I2C0_SCL/PWM_6B/IO13)
Pi_GPIO8_~CS0: J10.24 (~CE0/GPIO8), U13.28 (SPI0_CSn/U0RX/I2C0_SCL/PWM_0B/IO17), U17.2
Pi_GPIO9_MISO0: J10.21 (MISO0/GPIO9), U13.30 (SPI0_TX/U0RTS/I2C1_SCL/PWM_1B/IO19), U17.11
Pi_GPIO10_MOSI0: J10.19 (MOSI0/GPIO10), U13.27 (SPI0_RX/U0TX/I2C0_SDA/PWM_0A/IO16), U17.5
Pi_GPIO11_SCK0: J10.23 (SCLK0/GPIO11), U13.29 (SPI0_SCK/U0CTS/I2C1_SDA/PWM_1A/IO18), U17.14
Pi_GPIO12_PWM0: J10.32 (PWM0/GPIO12), U13.3 (SPI0_CSn/U0RX/I2C0_SCL/PWM_0B/IO1)
Pi_GPIO13_PWM1: J10.33 (PWM1/GPIO13), U13.4 (SPI0_SCK/U0CTS/I2C1_SDA/PWM_1A/IO2)
Pi_GPIO14_TXD: J10.8 (GPIO14/TXD), U13.11 (SPI1_RX/U0TX/I2C0_SDA/PWM_4A/IO8)
Pi_GPIO15_RXD: J10.10 (GPIO15/RXD), U13.12 (SPI1_CSn/U0RX/I2C0_SCL/PWM_4B/IO9)
Pi_GPIO16: J10.36 (GPIO16), U13.6 (SPI0_RX/U0TX/I2C0_SDA/PWM_2A/IO4)
Pi_GPIO17: J10.11 (GPIO17), U13.8 (SPI0_SCK/U0CTS/I2C1_SDA/PWM_3A/IO6)
Pi_GPIO18_PWM0: J10.12 (GPIO18/PWM0), U13.2 (SPI0_RX/U0TX/I2C0_SDA/PWM_0A/IO0)
Pi_GPIO19_MISO1: J10.35 (GPIO19/MISO1), U13.18 (SPI1_TX/U0RTS/I2C1_SCL/PWM_7B/IO15)
Pi_GPIO20_MOSI1: J10.38 (GPIO20/MOSI1), U13.15 (SPI1_RX/U0_TX/I2C0_SDA/PWM_6A/IO12)
Pi_GPIO21_SCK1: J10.40 (GPIO21/SCLK1), U13.17 (SPI1_SCK/U0CTS/I2C1_SDA/PWM_7A/IO14)
Pi_GPIO22: J10.15 (GPIO22), U13.7 (SPI0_CSn/U0RX/I2C0_SCL/PWM_2B/IO5)
Pi_GPIO23: J10.16 (GPIO23), U13.9 (SPI0_TX/U0RTS/I2C1_SCL/PWM_3B/IO7)
Pi_GPIO24: J10.18 (GPIO24), U13.31 (SPI0_RX/U1TX/I2C0_SDA/PWM_2A/IO20)
Pi_GPIO25: J10.22 (GPIO25), U13.5 (SPI0_TX/U0RTS/I2C1_SCL/PWM_1B/IO3)
Pi_GPIO26: J10.37 (GPIO26), U13.32 (SPI0_CSn/U1RX/I2C0_SCL/PWM_2B/IO21)
Pi_GPIO27: J10.13 (GPIO27), U13.34 (CLK_GPIN1/SPI0_SCK/U1CTS/I2C1_SDA/PWM_3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)
QSPI_SCK: U13.52 (QSPI_SCK), U14.6 (CLK)
QSPI_~SS: R33.1, U13.56 (SQPI_~SS), U14.1 (~CS)
SPI2ESP_MISO: U17.9
SPI2ESP_MOSI: U17.7
SPI2ESP_SCK: U17.12
SPI2ESP_~CS: U17.4
pico_SWCLK: U13.24 (SWCLK)
pico_SWDIO: U13.25 (SWDIO)
~USB_BOOT: R33.2, SW2.2
~USB_Host_PWR: Q5.1 (G)
~sw_SPI2ESP32: R53.2, U17.1 (IN)

Notes on the sheet:
Replacement part (smaller): W25Q16JWXHIQ -> 2x3mm XSON-8 packages
default HIGH
