MDCservice/EsPiFF/hardware/usb_uart.kicad_sch

## KiCad design hardware/usb_uart.kicad_sch (2022-10-01)

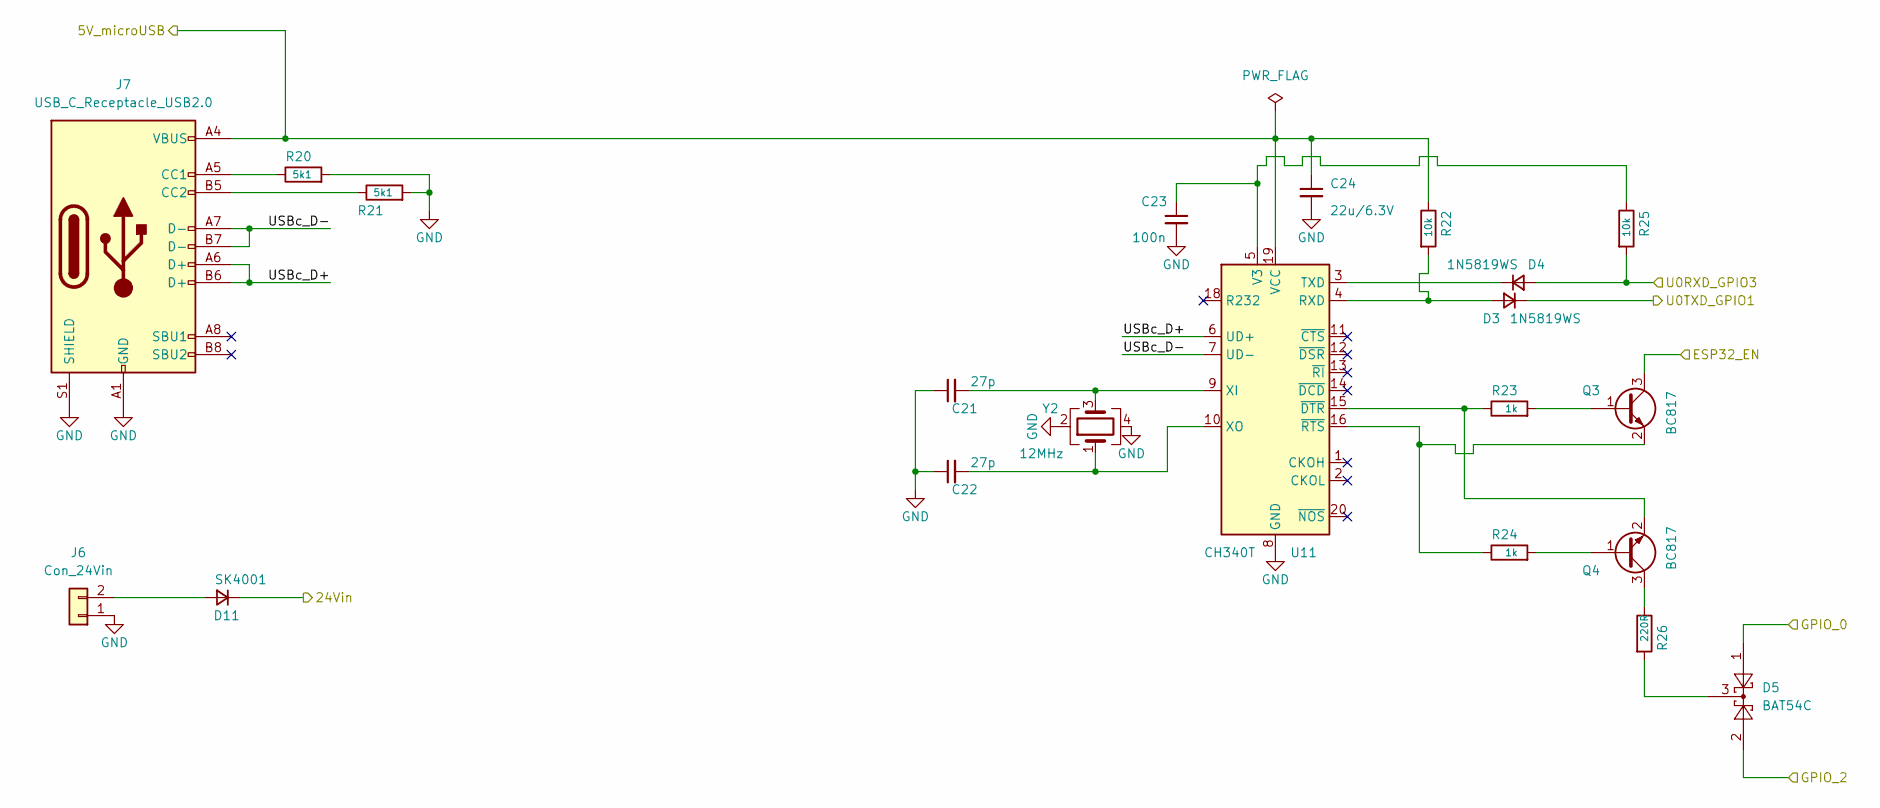
[picture p61: schematic usb_uart.kicad_sch]

Parts:
C21, C22: 27p; C_0603_1608Metric
C23: 100n; C_0603_1608Metric
C24: 22u/6.3V; C_0805_2012Metric
D3, D4: 1N5819WS; D_SOD-323
D5: BAT54C; SOT-23
D11: SK4001; D_SOD-123
J6: Con_24Vin; JST_EH_B2B-EH-A_1x02_P2.50mm_Vertical
J7: USB_C_Receptacle_USB2.0; USB_C_XKB_U262-16XN-4BVC11
Q3, Q4: BC817; SOT-23
R20, R21: 5k1; R_0603_1608Metric
R22, R25: 10k; R_0603_1608Metric
R23, R24: 1k; R_0603_1608Metric
R26: 220R; R_0603_1608Metric
U11: CH340T; SSOP-20_5.3x7.2mm_P0.65mm
Y2: 12MHz; Crystal_SMD_2520-4Pin_2.5x2.0mm

Connections:
5V_microUSB: C24.1, J7.A4 (VBUS), J7.A9 (VBUS), J7.B4 (VBUS), J7.B9 (VBUS), R22.1, U11.19 (VCC)
24Vin: D11.1 (K)
ESP32_EN: Q3.3 (C)
GND: C21.1, C22.1, C23.2, C24.2, J6.1, J7.A1 (GND), J7.A12 (GND), J7.B1 (GND), J7.B12 (GND), J7.S1 (SHIELD), R20.2, R21.2, U11.8 (GND), Y2.2, Y2.4
GPIO_0: D5.1
GPIO_2: D5.2
unnamed: C21.2, U11.9 (XI), Y2.3
unnamed: C22.2, U11.10 (XO), Y2.1
unnamed: C23.1, R25.1, U11.5 (V3)
unnamed: D3.2 (A), R22.2, U11.4 (RXD)
unnamed: D4.1 (K), U11.3 (TXD)
unnamed: D5.3, R26.2
unnamed: D11.2 (A), J6.2
unnamed: J7.A5 (CC1), R20.1
unnamed: J7.B5 (CC2), R21.1
unnamed: Q3.1 (B), R23.2
unnamed: Q3.2 (E), R24.1, U11.16 (~RTS)
unnamed: Q4.1 (B), R24.2
unnamed: Q4.2 (E), R23.1, U11.15 (~DTR)
unnamed: Q4.3 (C), R26.1
U0RXD_GPIO3: D4.2 (A), R25.2
U0TXD_GPIO1: D3.1 (K)
USBc_D+: J7.A6 (D+), J7.B6 (D+), U11.6 (UD+)
USBc_D-: J7.A7 (D-), J7.B7 (D-), U11.7 (UD-)
